RoboJackets/electrical-training/labs/week-4-schematic.kicad_sch

## KiCad design labs/week-4-schematic.kicad_sch (2023-10-12)

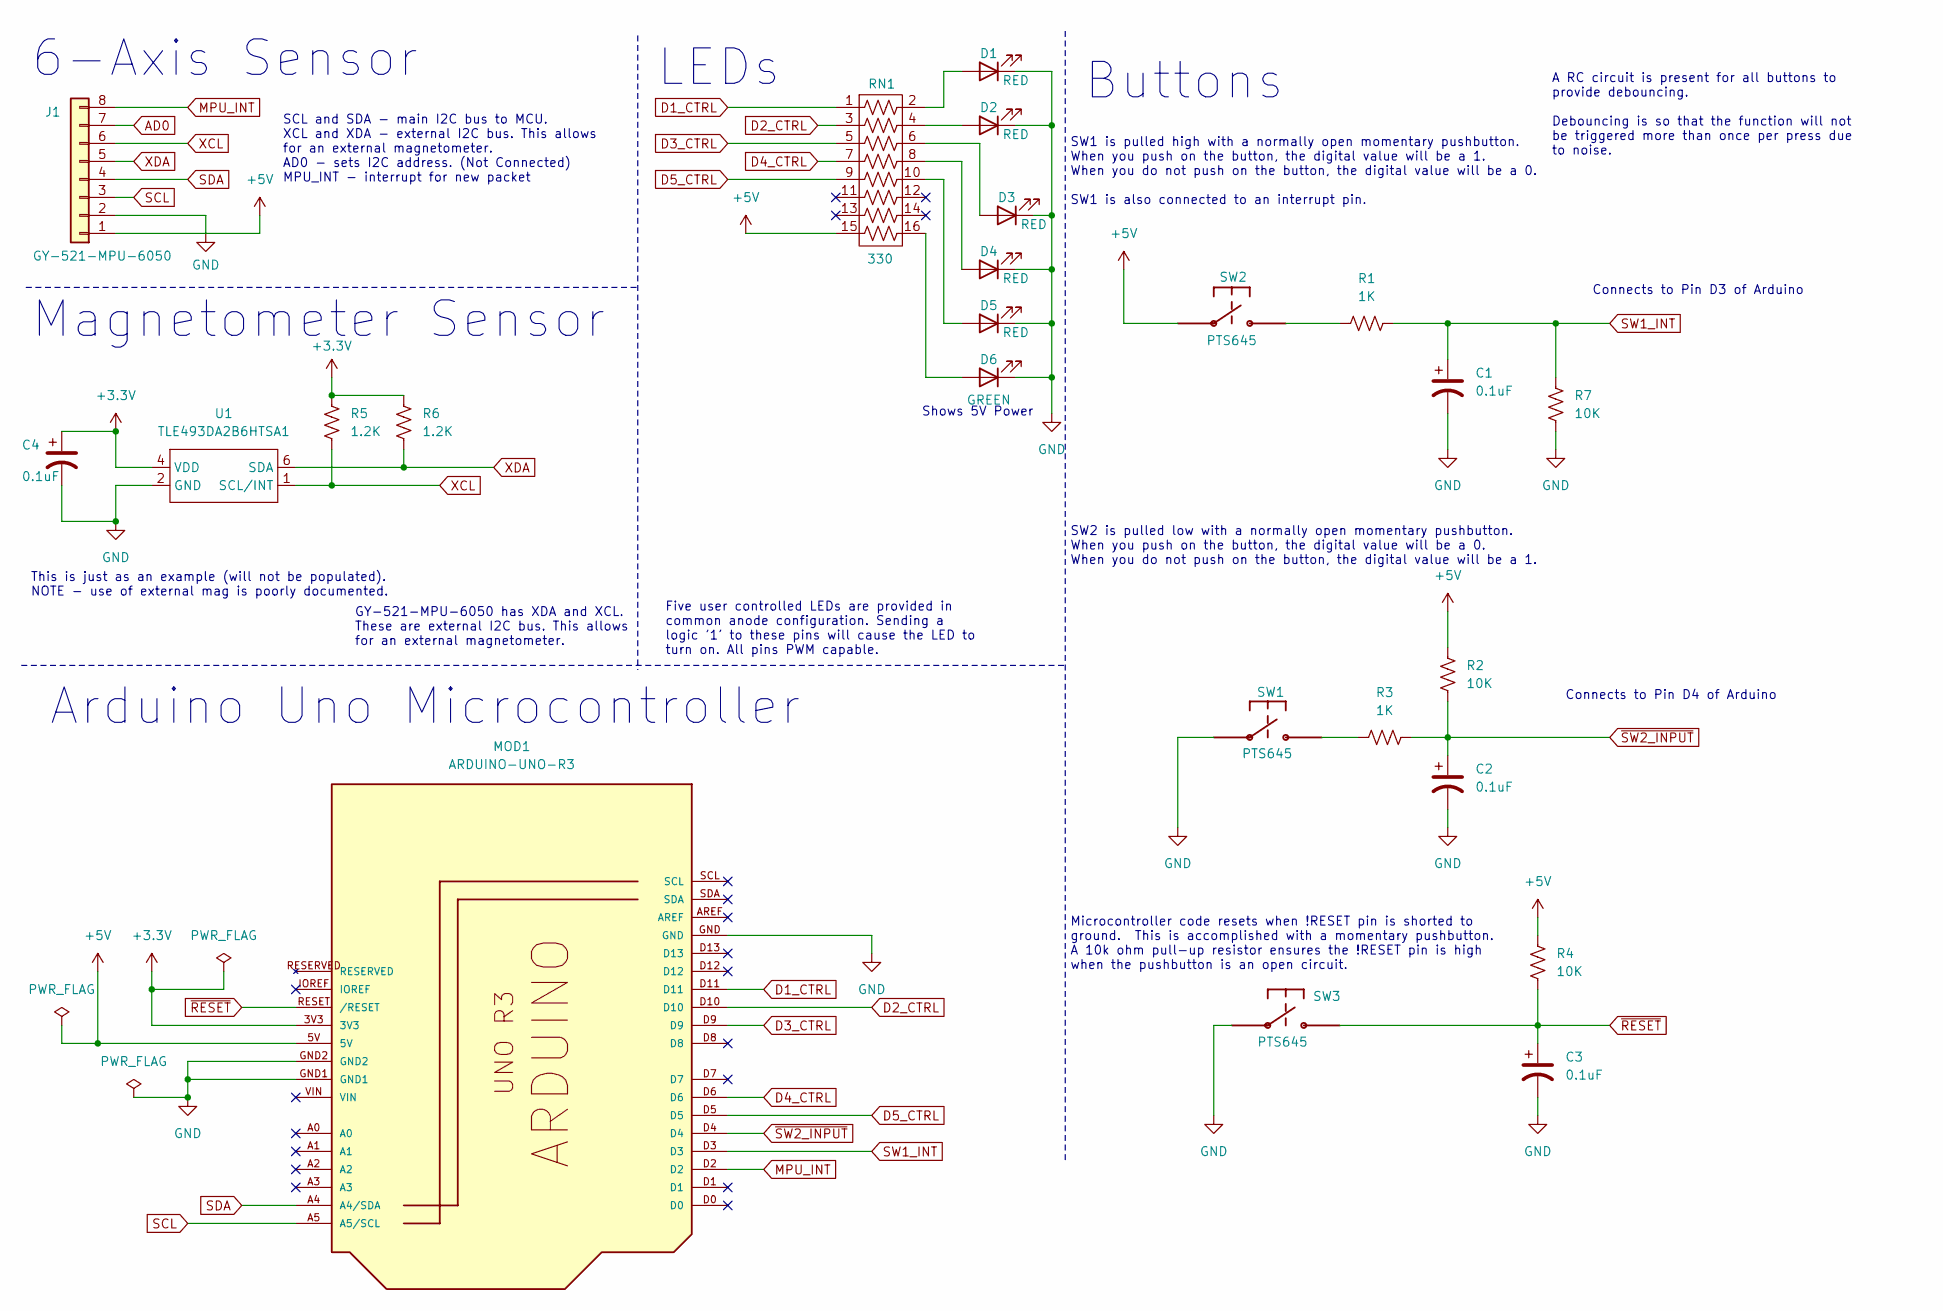
[picture p80: schematic week-4-schematic.kicad_sch]

Parts:
C1, C2, C3, C4: 0.1uF
D1, D2, D3, D4, D5: RED
D6: GREEN
J1: GY-521-MPU-6050
MOD1: ARDUINO-UNO-R3
R1, R3: 1K
R2, R4, R7: 10K
R5, R6: 1.2K
RN1: 330
SW1, SW2, SW3: PTS645; DIGIKEY CKN9112CT-ND
U1: TLE493DA2B6HTSA1

Connections:
+3.3V: C4.1, MOD1.3V3, R5.2, R6.1, U1.4 (VDD)
+5V: C1.2, C2.2, C3.2, C4.2, D1.1 (K), D2.1 (K), D3.1 (K), D4.1 (K), D5.1 (K), D6.1 (K), J1.1, J1.2, MOD1.5V, MOD1.GND, MOD1.GND1, MOD1.GND2, R2.1, R4.1, R7.2, RN1.15, SW1.1, SW1.2, SW2.1, SW2.2, SW3.1, SW3.2, U1.2 (GND), U1.3 (GND), U1.5 (GND)
AD0: J1.7
D1_CTRL: MOD1.D11, RN1.1
D2_CTRL: MOD1.D10, RN1.3
D3_CTRL: MOD1.D9, RN1.5
D4_CTRL: MOD1.D6, RN1.7
D5_CTRL: MOD1.D5, RN1.9
MPU_INT: J1.8, MOD1.D2
unnamed: D1.2 (A), RN1.2
unnamed: D2.2 (A), RN1.4
unnamed: D3.2 (A), RN1.6
unnamed: D4.2 (A), RN1.8
unnamed: D5.2 (A), RN1.10
unnamed: D6.2 (A), RN1.16
unnamed: R1.1, SW2.3, SW2.4
unnamed: R3.1, SW1.3, SW1.4
SCL: J1.3, MOD1.A5 (A5/SCL)
SDA: J1.4, MOD1.A4 (A4/SDA)
SW1_INT: C1.1, MOD1.D3, R1.2, R7.1
XCL: J1.6, R5.1, U1.1 (SCL/INT)
XDA: J1.5, R6.2, U1.6 (SDA)
~RESET: C3.1, MOD1.RESET (/RESET), R4.2, SW3.3, SW3.4
~SW2_INPUT: C2.1, MOD1.D4, R2.2, R3.2

Notes on the sheet:
Magnetometer Sensor
Shows 5V Power
SW1 is pulled high with a normally open momentary pushbutton. When you push on the button, the digital value will be a 1. When you do not push on the button, the digital value will be a 0. SW1 is also connected to an interrupt pin.
Buttons
Arduino Uno Microcontroller
This is just as an example (will not be populated). NOTE - use of external mag is poorly documented.
GY-521-MPU-6050 has XDA and XCL. These are external I2C bus. This allows for an external magnetometer.
LEDs
A RC circuit is present for all buttons to provide debouncing. Debouncing is so that the function will not be triggered more than once per press due to noise.
6-Axis Sensor
Connects to Pin D3 of Arduino
SCL and SDA - main I2C bus to MCU. XCL and XDA - external I2C bus. This allows for an external magnetometer. AD0 - sets I2C address. (Not Connected) MPU_INT - interrupt for new packet
Five user controlled LEDs are provided in common anode configuration. Sending a logic '1' to these pins will cause the LED to turn on. All pins PWM capable.
Connects to Pin D4 of Arduino
SW2 is pulled low with a normally open momentary pushbutton. When you push on the button, the digital value will be a 0. When you do not push on the button, the digital value will be a 1.
Microcontroller code resets when !RESET pin is shorted to ground. This is accomplished with a momentary pushbutton. A 10k ohm pull-up resistor ensures the !RESET pin is high when the pushbutton is an open circuit.
