RoboJackets/electrical-training/2024-2025/Week3/CopyAndPasteThisLab3.kicad_sch

## KiCad design 2024-2025/Week3/CopyAndPasteThisLab3.kicad_sch (2024-09-03)

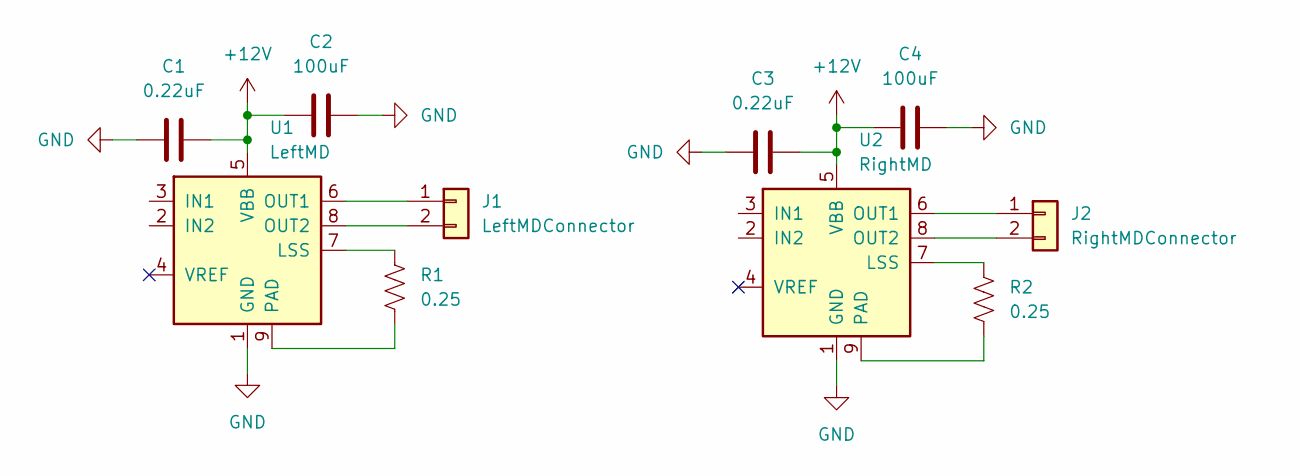
[picture p81: schematic CopyAndPasteThisLab3.kicad_sch]

Parts:
C1, C3: 0.22uF
C2, C4: 100uF
J1: LeftMDConnector
J2: RightMDConnector
R1, R2: 0.25
U1: LeftMD; SOIC-8-1EP_3.9x4.9mm_P1.27mm_EP2.41x3.3mm
U2: RightMD; SOIC-8-1EP_3.9x4.9mm_P1.27mm_EP2.41x3.3mm

Connections:
+12V: C1.2, C2.1, C3.2, C4.1, U1.5 (VBB), U2.5 (VBB)
GND: C1.1, C2.2, C3.1, C4.2, U1.1 (GND), U2.1 (GND)
unnamed: J1.1, U1.6 (OUT1)
unnamed: J1.2, U1.8 (OUT2)
unnamed: J2.1, U2.6 (OUT1)
unnamed: J2.2, U2.8 (OUT2)
unnamed: R1.1, U1.7 (LSS)
unnamed: R1.2, U1.9 (PAD)
unnamed: R2.1, U2.7 (LSS)
unnamed: R2.2, U2.9 (PAD)
