RoboJackets/electrical-training/2024-2025/Week4/ElectricalTrainingLab.kicad_sch

## KiCad design 2024-2025/Week4/ElectricalTrainingLab.kicad_sch (2024-09-03)

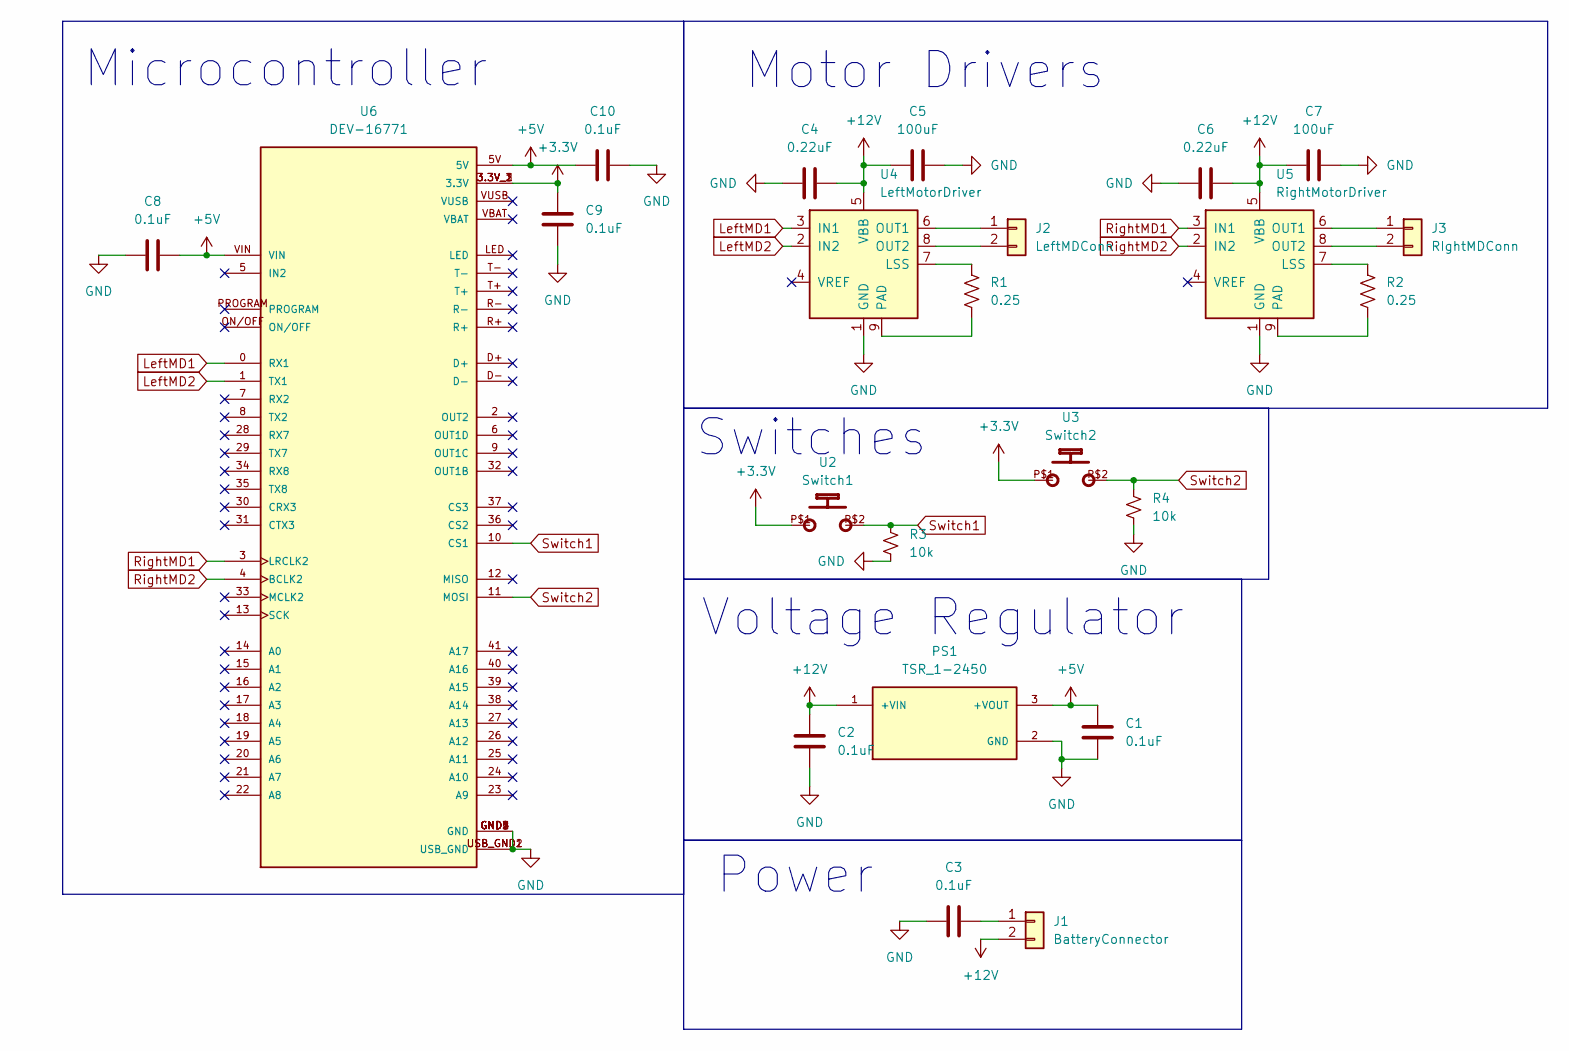
[picture p82: schematic ElectricalTrainingLab.kicad_sch]

Parts:
C1, C2, C3, C8, C9, C10: 0.1uF; C_0805_2012Metric_Pad1.18x1.45mm_HandSolder
C4, C6: 0.22uF; C_0805_2012Metric_Pad1.18x1.45mm_HandSolder
C5, C7: 100uF; C_0805_2012Metric_Pad1.18x1.45mm_HandSolder
J1: BatteryConnector; AMASS_XT60-F_1x02_P7.20mm_Vertical
J2: LeftMDConn; PhoenixContact_MSTBA_2,5_2-G_1x02_P5.00mm_Horizontal
J3: RIghtMDConn; PhoenixContact_MSTBA_2,5_2-G_1x02_P5.00mm_Horizontal
PS1: TSR_1-2450; Converter_DCDC_TRACO_TSR-1_THT; PARTREV Apr 27, 2020
R1, R2: 0.25; R_0805_2012Metric_Pad1.20x1.40mm_HandSolder
R3, R4: 10k; R_0805_2012Metric_Pad1.20x1.40mm_HandSolder
U2: Switch1; CHERRY_MX1A-11NN_SWITCH
U3: Switch2; CHERRY_MX1A-11NN_SWITCH
U4: LeftMotorDriver; SOIC-8-1EP_3.9x4.9mm_P1.27mm_EP2.41x3.3mm
U5: RightMotorDriver; SOIC-8-1EP_3.9x4.9mm_P1.27mm_EP2.41x3.3mm
U6: DEV-16771; MODULE_DEV-16771; PARTREV 4.1

Connections:
+3.3V: C9.1, U2.P$1, U3.P$1, U6.3.3V_1 (3.3V), U6.3.3V_2 (3.3V), U6.3.3V_3 (3.3V)
+5V: C1.1, C8.1, C10.2, PS1.3 (+VOUT), U6.5V, U6.VIN
+12V: C2.1, C4.2, C5.1, C6.2, C7.1, J1.2, PS1.1 (+VIN), U4.5 (VBB), U5.5 (VBB)
GND: C1.2, C2.2, C3.1, C4.1, C5.2, C6.1, C7.2, C8.2, C9.2, C10.1, PS1.2 (GND), R3.2, R4.2, U4.1 (GND), U5.1 (GND), U6.GND1 (GND), U6.GND2 (GND), U6.GND3 (GND), U6.GND4 (GND), U6.GND5 (GND), U6.USB_GND1 (USB_GND), U6.USB_GND2 (USB_GND)
LeftMD1: U4.3 (IN1), U6.0 (RX1)
LeftMD2: U4.2 (IN2), U6.1 (TX1)
unnamed: C3.2, J1.1
unnamed: J2.1, U4.6 (OUT1)
unnamed: J2.2, U4.8 (OUT2)
unnamed: J3.1, U5.6 (OUT1)
unnamed: J3.2, U5.8 (OUT2)
unnamed: R1.1, U4.7 (LSS)
unnamed: R1.2, U4.9 (PAD)
unnamed: R2.1, U5.7 (LSS)
unnamed: R2.2, U5.9 (PAD)
RightMD1: U5.3 (IN1), U6.3 (LRCLK2)
RightMD2: U5.2 (IN2), U6.4 (BCLK2)
Switch1: R3.1, U2.P$2, U6.10 (CS1)
Switch2: R4.1, U3.P$2, U6.11 (MOSI)

Notes on the sheet:
Microcontroller
Power
Voltage Regulator
Switches
Motor Drivers
